SchwarzeLanzenreiter/MotoRecoPico/firmware/src/nmea.h

// MIT License
//
// Copyright (c) 2026 Schwarze Lanzenreiter
//
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
#ifndef NMEA_H
#define NMEA_H

#include <stdint.h>
#include <stddef.h>

// NMEA 0183 parser. the pi version got all of this from gpsd, which does not exist here, so GGA
// and RMC are parsed directly off the module's serial stream.
//
// GGA and RMC each carry a part of what the log needs, so the state below is the union of the two
// and is updated in place, the same way gpsd merged them into one fix

#ifdef __cplusplus
extern "C" {
#endif

// the standard caps a sentence at 82 bytes including "$" and CRLF. accept a little more so a
// chatty module does not make every sentence look broken
#define NMEA_MAX_SENTENCE 120

enum {
	NMEA_RESULT_INVALID = -1,	// bad framing or checksum. sentence was dropped
	NMEA_RESULT_IGNORED = 0,	// well formed, but not a sentence we use
	NMEA_RESULT_GGA     = 1,
	NMEA_RESULT_RMC     = 2,
	NMEA_RESULT_GSA     = 3,	// fix mode and dilution of precision
	NMEA_RESULT_GSV     = 4		// satellites in view and their signal strength
};

// GSV comes as a series of sentences per constellation, so the counts have to be accumulated
// across a cycle before they mean anything. one slot per talker (GP, GL, GA, ...)
#define NMEA_MAX_TALKERS 4

typedef struct {
	char	id[3];			// talker, e.g. "GP". empty slot while id[0] == 0
	int		in_view;		// last completed cycle
	int		tracked;		// of those, how many report a signal to noise ratio
	int		best_snr;
	int		acc_tracked;	// cycle in progress
	int		acc_best_snr;
} nmea_gsv_t;

typedef struct {
	int		has_fix;		// GGA quality > 0, or RMC status 'A'
	double	latitude;		// degrees, north positive
	double	longitude;		// degrees, east positive

	int		has_altitude;	// GGA carried an MSL altitude. false while the fix is 2D only
	double	altitude;		// metres above mean sea level

	int		has_speed;		// RMC carried a speed over ground
	double	speed;			// metres per second, like gpsd's fix.speed

	int		has_time;		// RMC carried a valid date and time
	int64_t	unix_time;		// seconds since the epoch, UTC

	// everything below is diagnostics only. none of it reaches the .dat file, it exists to answer
	// "why is there still no fix": a receiver that sees no satellites at all is a different
	// problem from one that sees eight but cannot resolve them
	int		quality;		// GGA field 6 as received: 0 none, 1 GPS, 2 DGPS, 4/5 RTK
	int		sats_used;		// GGA field 7
	double	hdop;			// GGA field 8. 0 when not reported
	int		fix_mode;		// GSA field 2: 1 none, 2 2D, 3 3D
	double	pdop;			// GSA
	double	vdop;			// GSA

	nmea_gsv_t gsv[NMEA_MAX_TALKERS];
} nmea_fix_t;

// totals across every constellation the receiver reports
int nmea_sats_in_view(const nmea_fix_t *fix);
int nmea_sats_tracked(const nmea_fix_t *fix);
int nmea_best_snr(const nmea_fix_t *fix);

// assembles bytes from the UART into complete sentences
typedef struct {
	char	buf[NMEA_MAX_SENTENCE + 1];
	size_t	len;
	int		overrun;		// current line was too long. drop it at the terminator
} nmea_reader_t;

void nmea_init(nmea_fix_t *fix);
void nmea_reader_init(nmea_reader_t *reader);

// feeds one received byte. returns a NUL terminated sentence when one completes, else NULL.
// the returned pointer is owned by the reader and stays valid until the next call
const char *nmea_reader_push(nmea_reader_t *reader, char c);

// parses one sentence into fix. returns one of NMEA_RESULT_*
int nmea_parse(nmea_fix_t *fix, const char *sentence);

// helpers exposed for the host tests
int nmea_checksum_ok(const char *sentence);
int64_t nmea_to_unix(int year, int month, int day, int hour, int min, int sec);

#ifdef __cplusplus
}
#endif

#endif // NMEA_H
